psy0rz/meowton/3d/catscale/drawing.png

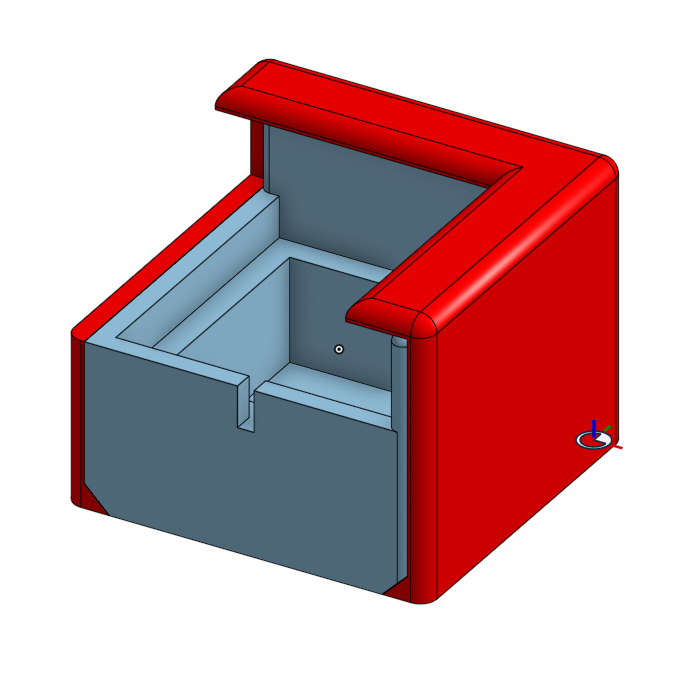
3d/catscale/drawing.png
