psy0rz/meowton/3d/catscale/loadcell shop.png

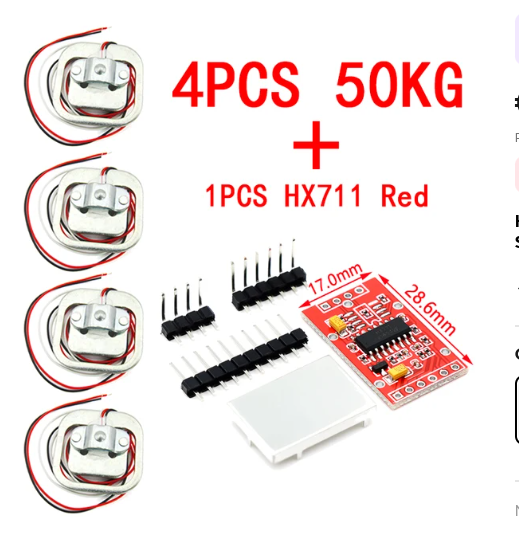
3d/catscale/loadcell shop.png
