psy0rz/meowton/3d/catscale/loadcell.jpg

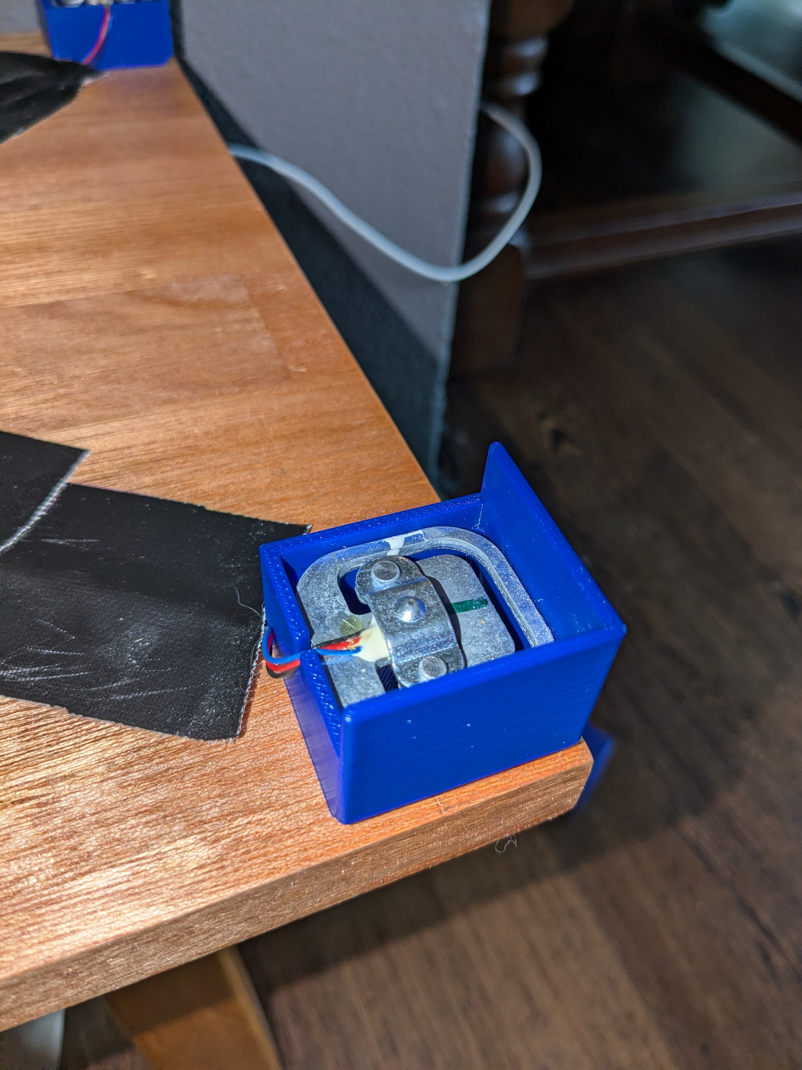
3d/catscale/loadcell.jpg
