psy0rz/meowton/3d/catscale/stopper.png

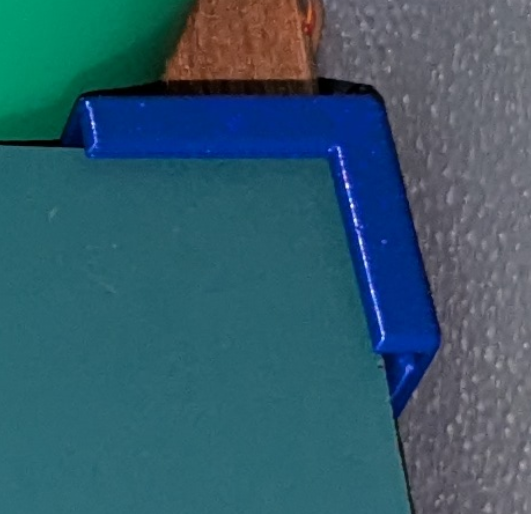
3d/catscale/stopper.png
