psy0rz/meowton/3d/dispenser/above.jpg

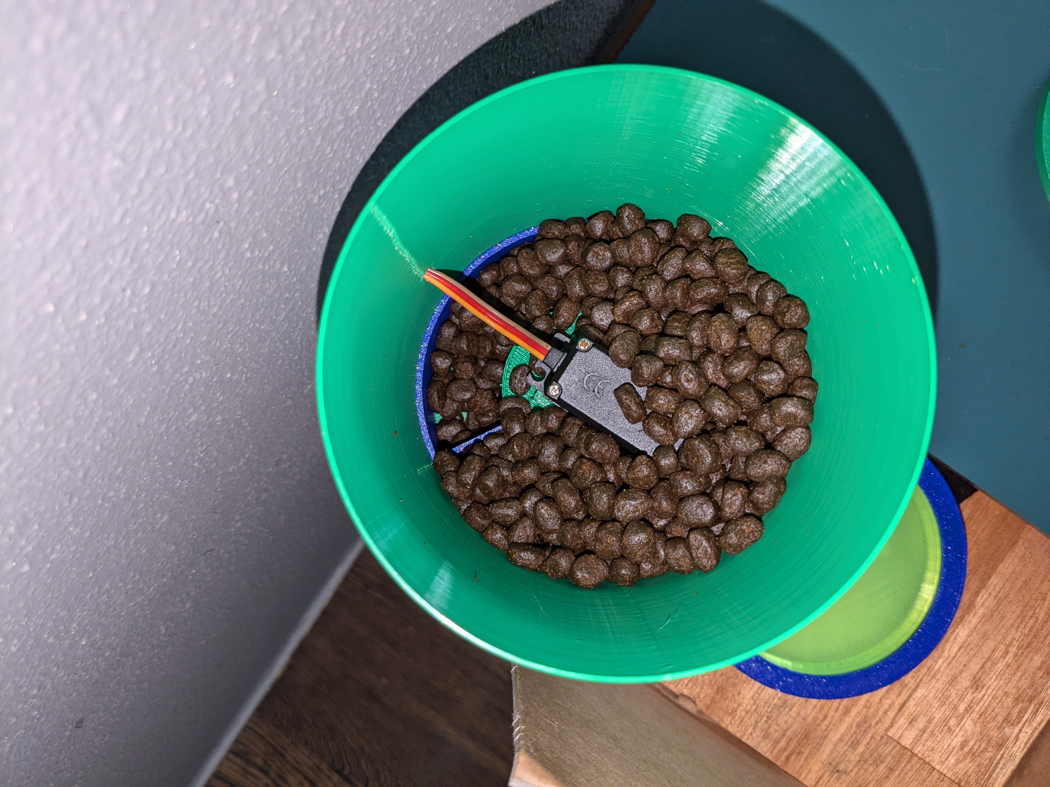
3d/dispenser/above.jpg
