psy0rz/meowton/3d/dispenser/drawing.png

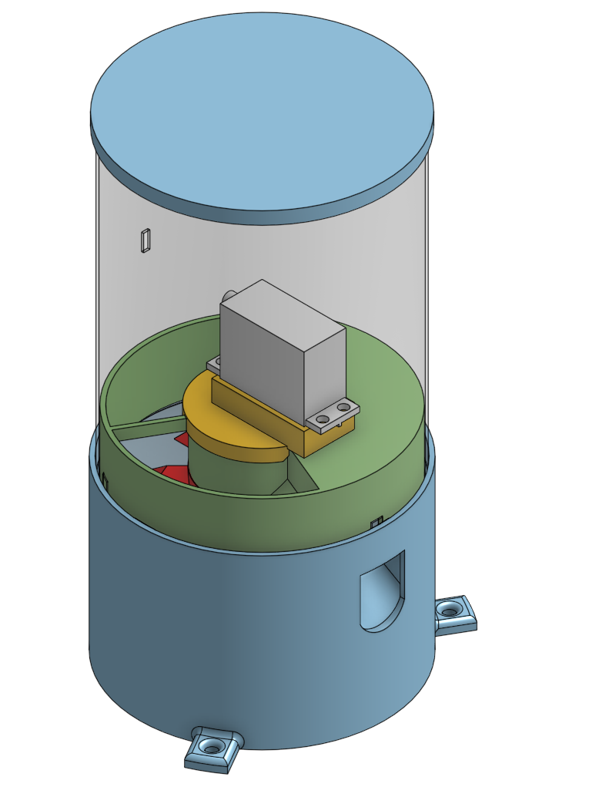
3d/dispenser/drawing.png
