psy0rz/meowton/3d/dispenser/exploded.png

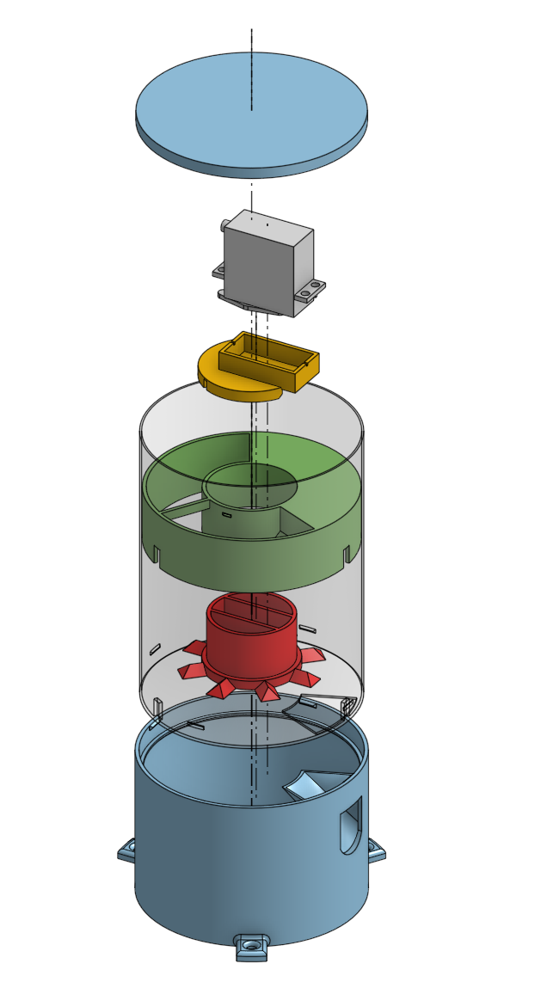
3d/dispenser/exploded.png
