psy0rz/meowton/3d/dispenser/front.jpg

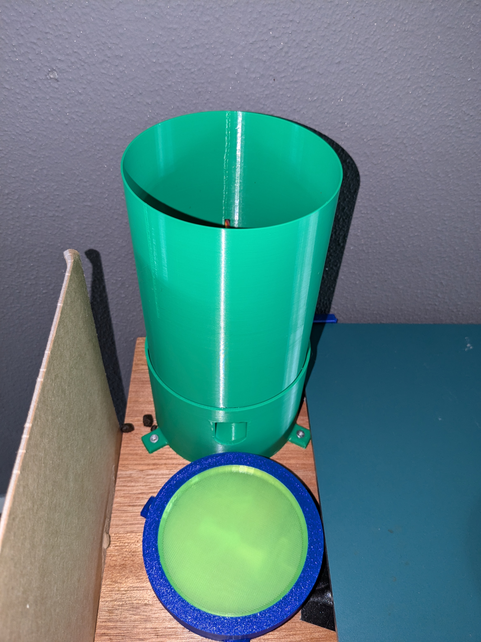
3d/dispenser/front.jpg
