psy0rz/meowton/3d/foodscale/bowl.jpg

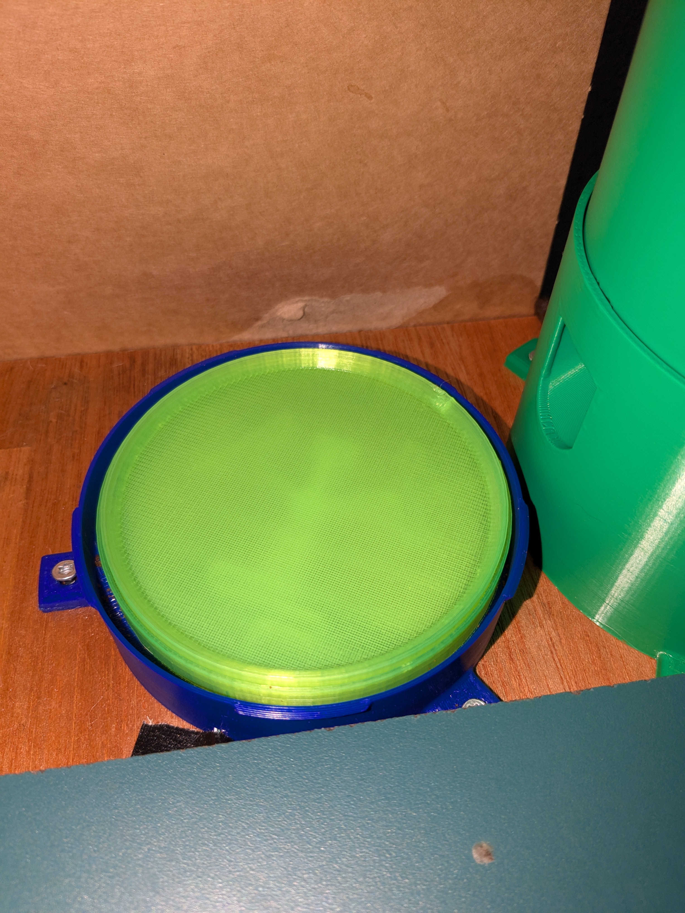
3d/foodscale/bowl.jpg
