psy0rz/meowton/3d/foodscale/complete.jpg

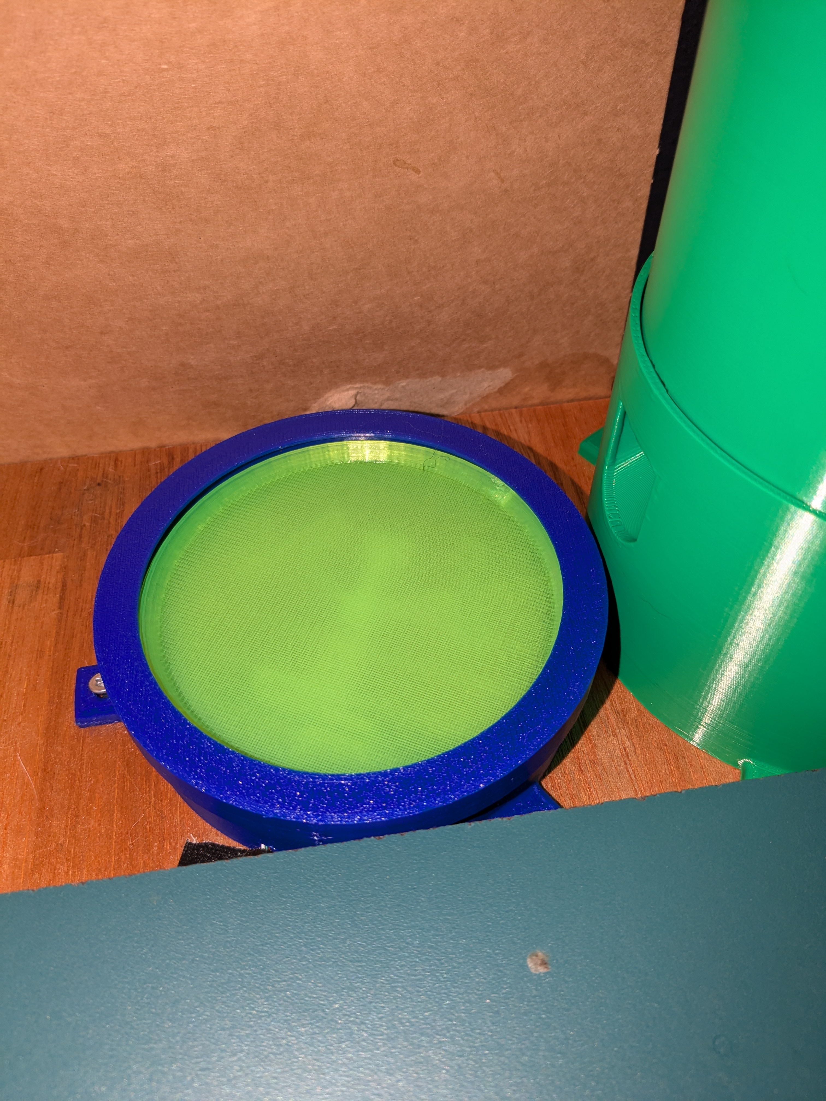
3d/foodscale/complete.jpg
