psy0rz/meowton/3d/foodscale/drawing.png

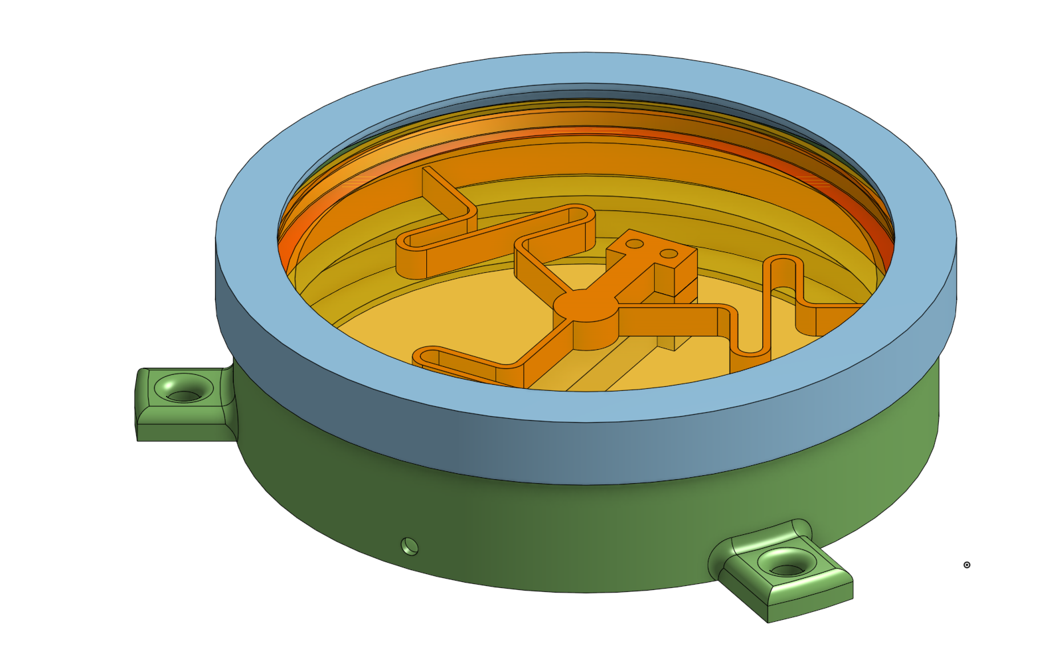
3d/foodscale/drawing.png
