psy0rz/meowton/3d/foodscale/exploded.png

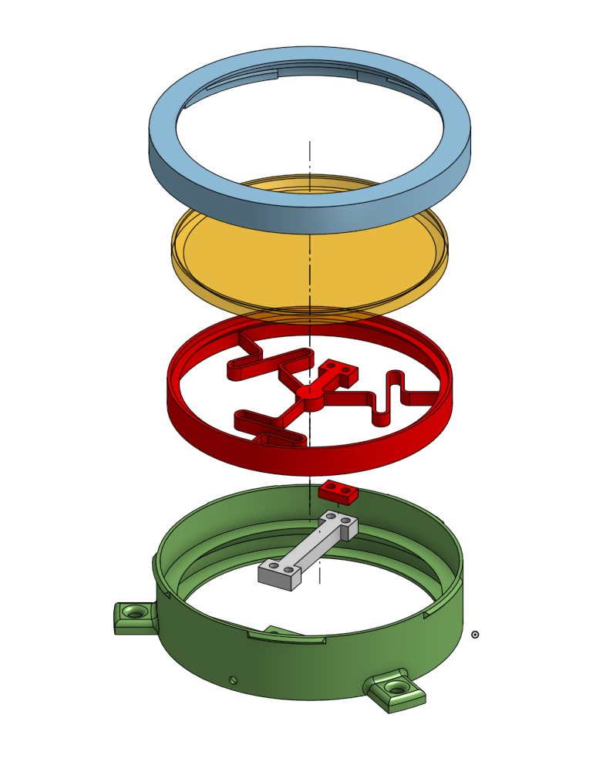
3d/foodscale/exploded.png
