psy0rz/meowton/3d/foodscale/inside.jpg

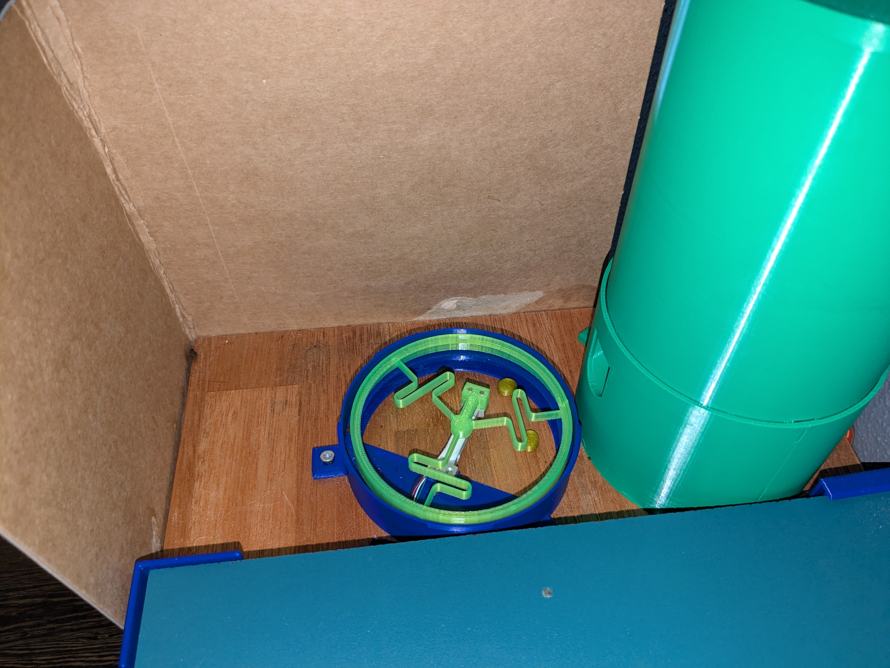
3d/foodscale/inside.jpg
