psy0rz/meowton/3d/foodscale/loadcell.png

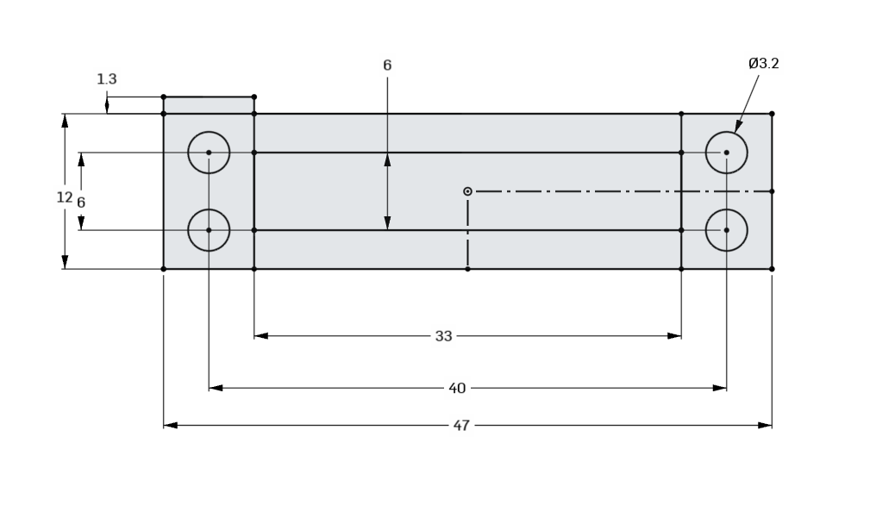
3d/foodscale/loadcell.png
