psy0rz/meowton/3d/foodsize.jpg

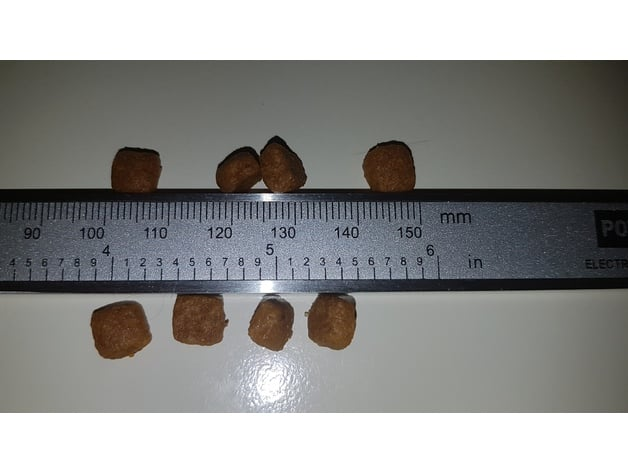
3d/foodsize.jpg
