psy0rz/meowton/3d/mogwai.jpg

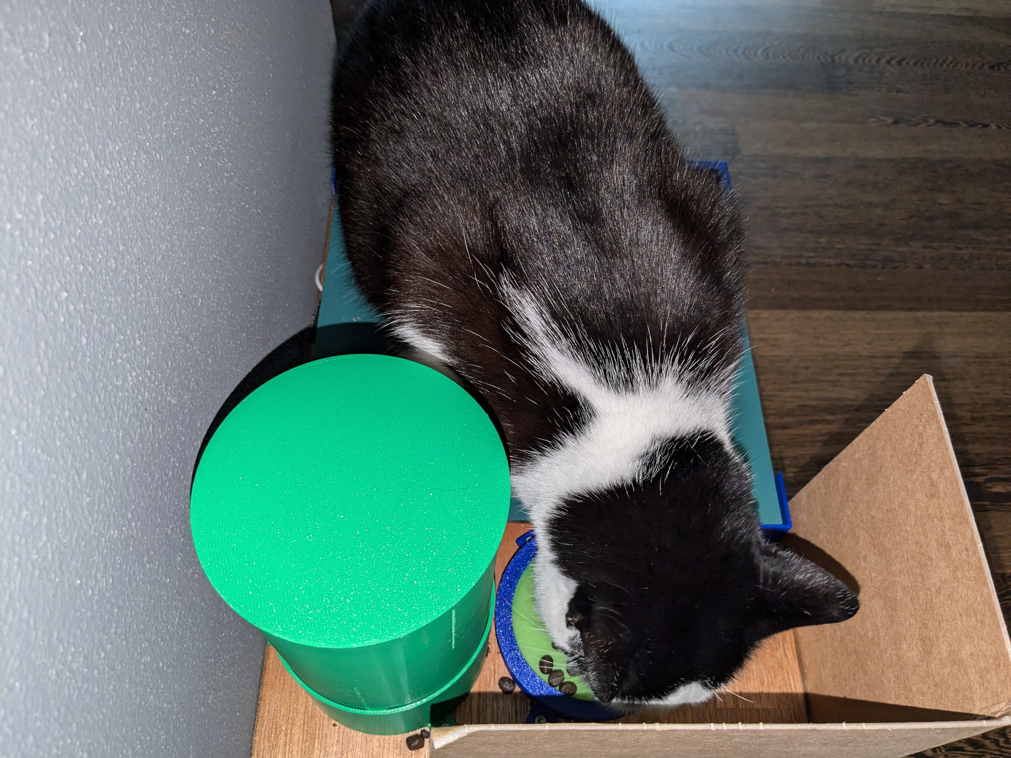
3d/mogwai.jpg
