psy0rz/meowton/3d/software/feeder.png

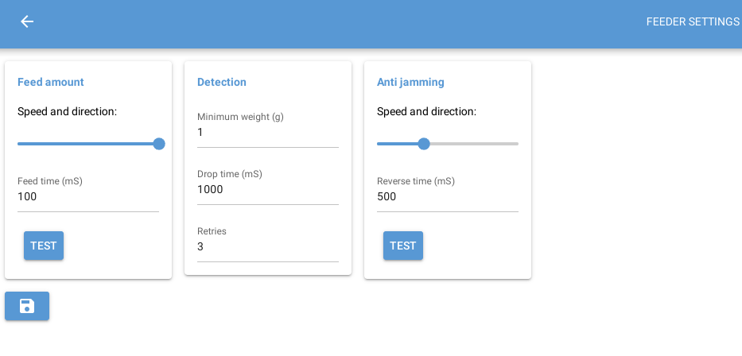
3d/software/feeder.png
