psy0rz/meowton/3d/software/graph.png

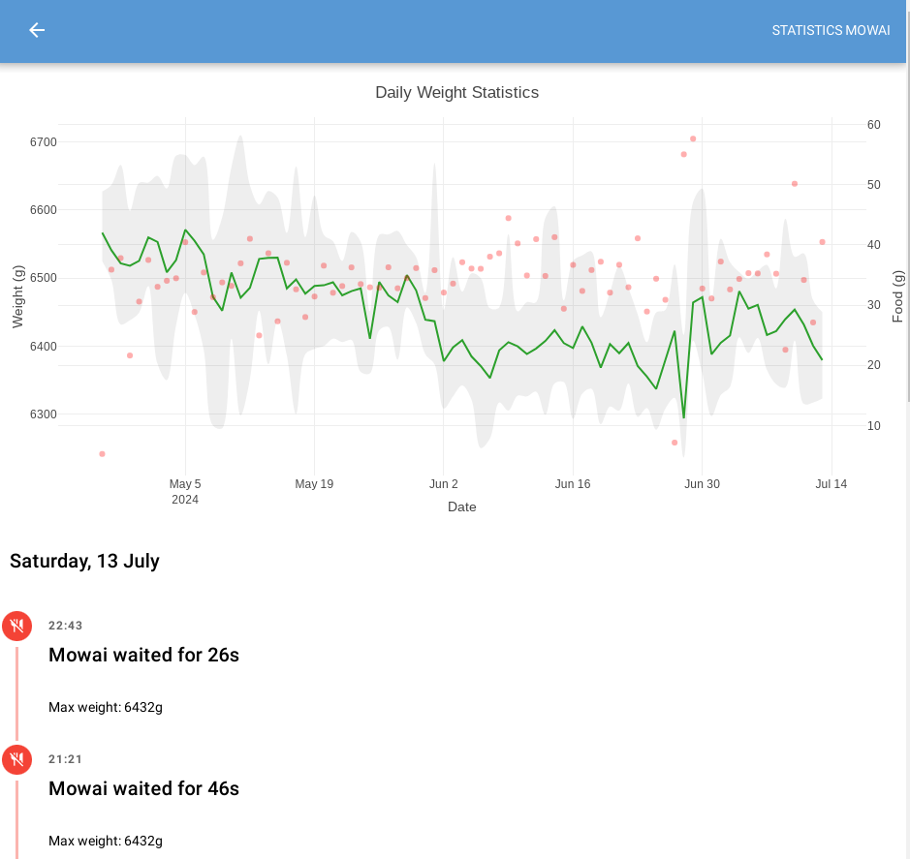
3d/software/graph.png
