psy0rz/meowton/3d/software/main.png

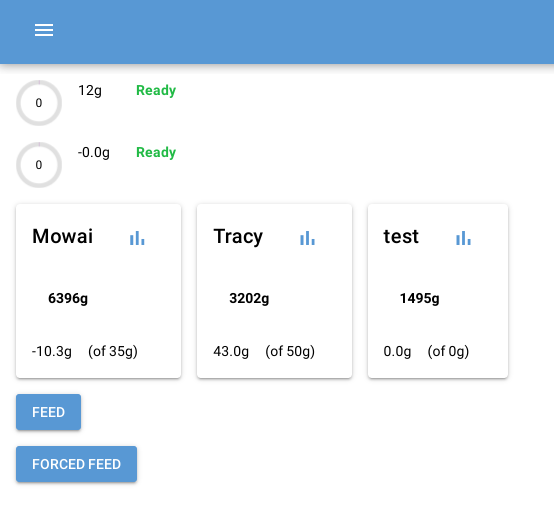
3d/software/main.png
