psy0rz/meowton/3d/software/schedule.png

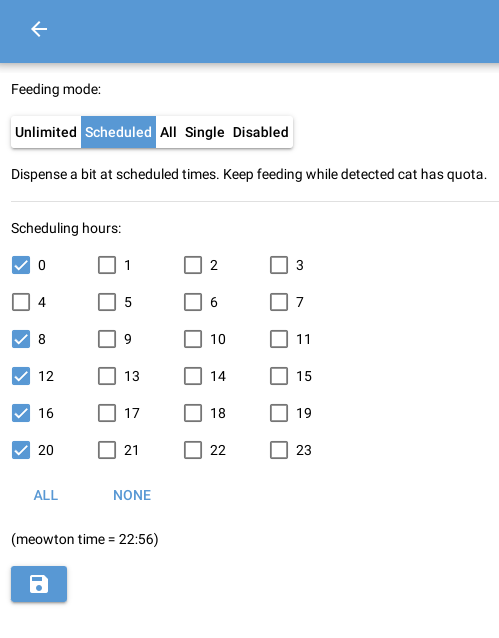
3d/software/schedule.png
