psy0rz/meowton/3d/software/calibration.png

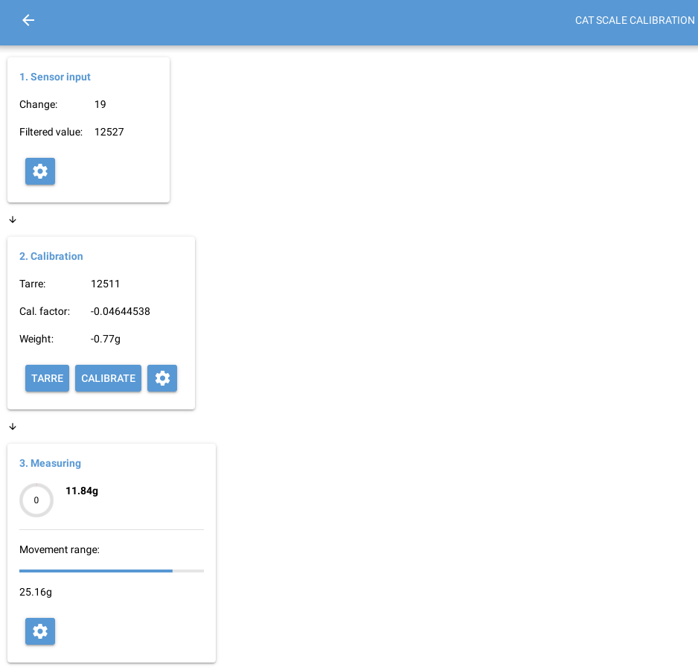
3d/software/calibration.png
