psy0rz/meowton/src/meowton.py

import asyncio
from pprint import pprint

import db
import settings
from cat_detector import CatDetector
from feeder import Feeder
from food_counter import FoodCounter
from food_scheduler import FoodScheduler
from scale import Scale
from sensor_reader import SensorReader
from status_led import StatusLed


# NOTE: my catfood weigh aprox 0.33g per piece

class Meowton:
    """main class that instantiates the other classes and tasks"""
    food_reader: SensorReader
    food_scale: Scale
    food_counter: FoodCounter
    food_scheduler: FoodScheduler
    feeder: Feeder
    status_led: StatusLed

    cat_reader: SensorReader
    cat_scale: Scale
    cat_detector: CatDetector

    def __init__(self, sim: bool):

        self.init_food(sim)
        self.init_cat(sim)
        self.status_led=StatusLed()



    # food scale stuff and default settings
    def init_food(self, sim):
        name = 'food'

        ( self.food_scale, created) = Scale.get_or_create(name=name, stable_range=0.1, stable_range_perc=0, stable_measurements=2, stable_auto_tarre_count=0.1, stable_auto_tarre_max=0.1)
        if created:
            self.food_scale.sensor_filter.filter_diff=10000
            self.food_scale.sensor_filter.save()

        self.food_reader = SensorReader(name, 23, 24, sim, self.food_scale.measurement)
        self.food_counter = FoodCounter()

        self.food_scheduler = FoodScheduler.get_or_none(id=1)
        if self.food_scheduler is None:
            self.food_scheduler = FoodScheduler.create()

        self.feeder = Feeder.get_or_create(id=1)[0]
        self.feeder.init(self.food_scale)

    # cat scale stuff and default settings
    def init_cat(self, sim):
        name = 'cat'

        ( self.cat_scale, created) = Scale.get_or_create(name=name, stable_range=30, stable_range_perc=1, stable_measurements=10, stable_auto_tarre_count=0.1, stable_auto_tarre_max=200)
        if created:

            self.cat_scale.sensor_filter.filter_diff=1000
            self.cat_scale.sensor_filter.save()

        self.cat_reader = SensorReader(name, 27, 17, sim, self.cat_scale.measurement)
        self.cat_detector = CatDetector()

    async def start(self):


        tasks=[]

        self.food_reader.start()
        self.cat_reader.start()

        tasks.append(asyncio.create_task(self.cat_detector.task(self.cat_scale)))
        tasks.append(asyncio.create_task(self.feeder.task()))
        tasks.append(asyncio.create_task(self.food_counter.task(self.food_scale, self.feeder, self.cat_detector)))
        tasks.append(asyncio.create_task(self.food_scheduler.task(self.feeder, self.cat_detector)))

        tasks.append(asyncio.create_task(self.status_led.task(self.feeder, self.cat_detector)))

        return tasks

    def stop(self):
        self.food_reader.stop()
        self.cat_reader.stop()


meowton = Meowton(settings.dev_mode)
