psy0rz/meowton/micropython/displayio.py

import timer

from machine import I2C, Pin
from esp8266_i2c_lcd import I2cLcd

class DisplayIO():

    def __init__(self):
        DEFAULT_I2C_ADDR = 0x27
        self.i2c = I2C(scl=Pin(22), sda=Pin(21), freq=400000)

        self.cols=20
        self.rows=4
        # 2x16
        # self.lcd = I2cLcd(self.i2c, DEFAULT_I2C_ADDR, 2, 16)

        # 4x16
        self.lcd = I2cLcd(self.i2c, DEFAULT_I2C_ADDR, self.rows, self.cols)

        self.cats=[]
        self.msg_timeout=0


    def scale_weight_stable(self, weight):
        self.lcd.move_to(0,0)
        s=" {:4.0f}g cat".format(weight)
        s="{:<10}".format(s)
        self.lcd.putstr(s)

    def scale_weight_unstable(self):
        self.lcd.move_to(0,0)
        self.lcd.putstr("*")


    def food_weight_stable(self, weight):
        self.lcd.move_to(11,0)
        s=" {:2.0f}g food".format(weight)
        s="{:<9}".format(s)
        self.lcd.putstr(s)

    def food_weight_unstable(self):
        self.lcd.move_to(11,0)
        self.lcd.putstr("*")


    def update_cat(self, cat):

        # if cat:
        #     if cat.state.name!=self.last_cat:
        #         self.last_cat=cat.state.name
        #         self.cat_row=self.cat_row+1
        #         if self.cat_row>3:
        #             self.cat_row=2
        if cat and cat not in self.cats:
            self.cats.append(cat)

            #max 2 cats on display
            self.cats=self.cats[-2:]


    def refresh(self):
        self.lcd.move_to(0,2)
        for cat in self.cats:
            if cat.state.weight:
                # s="{:<6} {:4.0f}g {:7.3f}".format(cat.state.name[:8], cat.state.weight,  cat.get_quota())
                s="{:<6} {:4.0f}g {:5.0f}m".format(cat.state.name[:8], cat.state.weight, cat.time())
                s="{:<20}".format(s)
                self.lcd.putstr(s)

        if self.msg_timeout and timer.diff(timer.timestamp,self.msg_timeout)>0:
            self.lcd.move_to(0,1)
            self.lcd.putstr("{:<20}".format(""))
            self.msg_timeout=None




    def msg(self, txt, timeout=10):
        self.lcd.move_to(0,1)
        self.lcd.putstr("{:<20}".format(txt[:20]))
        if timeout:
            self.msg_timeout=timer.add(timer.timestamp, timeout*1000)
        else:
            self.msg_timeout=None
